yu-mingfu/FPGA_EP4CE6E22C8N_Board/images/image-20230428082345950.png

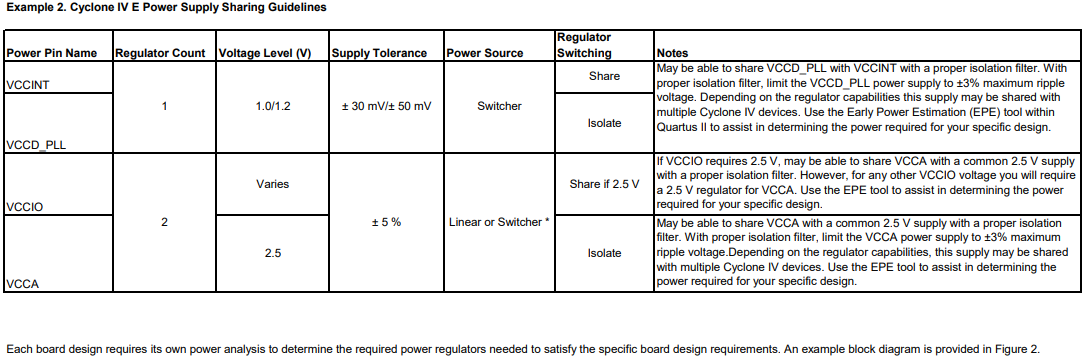
images/image-20230428082345950.png
